c-coyne/logic-pro-transport-controller/doc/architecture/SystemElectricalSchematic.kicad_sch

## KiCad design doc/architecture/SystemElectricalSchematic.kicad_sch (2024-03-14)

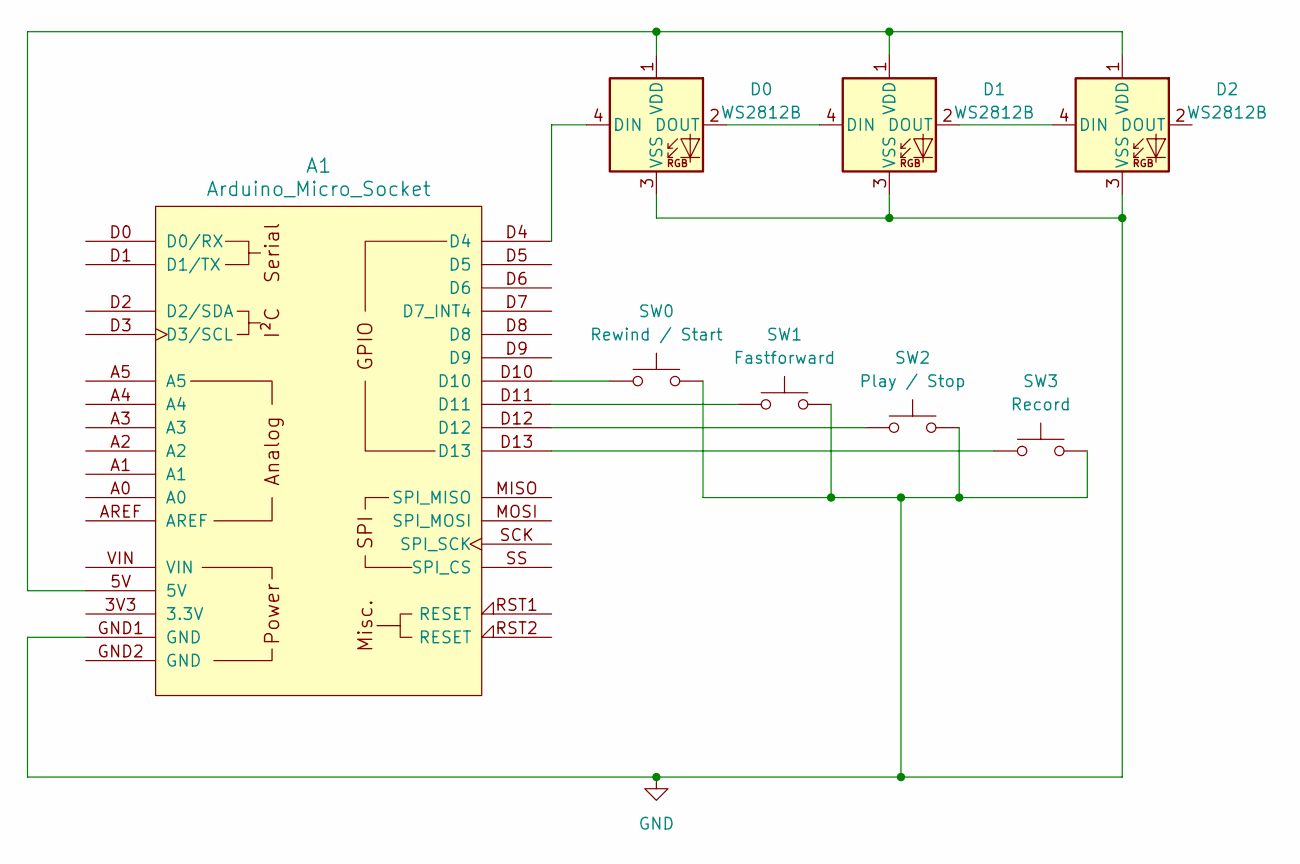
[picture p21: schematic SystemElectricalSchematic.kicad_sch]

Parts:
A1: Arduino_Micro_Socket
D0, D1, D2: WS2812B; LED_WS2812B_PLCC4_5.0x5.0mm_P3.2mm
SW0: Rewind / Start
SW1: Fastforward
SW2: Play / Stop
SW3: Record

Connections:
GND: A1.GND1 (GND), D0.3 (VSS), D1.3 (VSS), D2.3 (VSS), SW0.2, SW1.2, SW2.2, SW3.2
unnamed: A1.5V, D0.1 (VDD), D1.1 (VDD), D2.1 (VDD)
unnamed: A1.D4, D0.4 (DIN)
unnamed: A1.D10, SW0.1
unnamed: A1.D11, SW1.1
unnamed: A1.D12, SW2.1
unnamed: A1.D13, SW3.1
unnamed: D0.2 (DOUT), D1.4 (DIN)
unnamed: D1.2 (DOUT), D2.4 (DIN)
