c-coyne/logic-pro-transport-controller/include/Footswitch.h

/*=====================================================================================*\
| Author:   Christopher Coyne                                         March 13th, 2024  |
| --------------------------------------------------------------------------------------|
| Date:     March 13th, 2024                                                            |
| --------------------------------------------------------------------------------------|
| MODULE:     [ Footswitch ]                                                            |
| --------------------------------------------------------------------------------------|
| DESCRIPTION:                                                                          |
|    Footswitch class                                                                   |
| --------------------------------------------------------------------------------------|
\*=====================================================================================*/

#ifndef FOOTSWITCH_H
#define FOOTSWITCH_H

/****************************************************
 *  Include files                                   *
 ****************************************************/
#include "Switch.h"
#include "Cfg_Types.h"

/****************************************************
 *  Class definition                                *
 ****************************************************/

class Footswitch {
    private:
        Switch switch0;
        Switch switch1;
        Switch switch2;
        Switch switch3;
    public:
        Footswitch(int switchPins[4]);
        ~Footswitch();
        SwitchID checkSwitches();
};

#endif // FOOTSWITCH_H
