c-coyne/logic-pro-transport-controller/include/Switch.h

/*=====================================================================================*\
| Author:   Christopher Coyne                                         March 13th, 2024  |
| --------------------------------------------------------------------------------------|
| MODULE:     [ Switch ]                                                                |
| --------------------------------------------------------------------------------------|
| DESCRIPTION:                                                                          |
|    Switch class                                                                       |
| --------------------------------------------------------------------------------------|
\*=====================================================================================*/

#ifndef SWITCH_H
#define SWITCH_H

/****************************************************
 *  Class definition                                *
 ****************************************************/

class Switch {
    private:
        int id;
        int pin;
    public:
        Switch(int idValue, int pinValue);
        ~Switch();
        bool isPressed();
};

#endif // SWITCH_H
