c-coyne/logic-pro-transport-controller/src/Switch.cpp

/*=====================================================================================*\
| Author:   Christopher Coyne                                         March 13th, 2024  |
| --------------------------------------------------------------------------------------|
| MODULE:     [ Switch ]                                                                |
| --------------------------------------------------------------------------------------|
| DESCRIPTION:                                                                          |
|    Switch class                                                                       |
| --------------------------------------------------------------------------------------|
\*=====================================================================================*/

/****************************************************
 *  Include files                                   *
 ****************************************************/
#include "Switch.h"
#include <Arduino.h>

/****************************************************
 *  Constructor / destructor                        *
 ****************************************************/

Switch::Switch(int idValue, int pinValue) : id(idValue), pin(pinValue) {}

Switch::~Switch() {}

/****************************************************
 *  Member functions                                *
 ****************************************************/

bool Switch::isPressed() {
    return (digitalRead(pin) == LOW) ? true : false;
}
